LazarevMike/GarMen_StepTracker/Analogue filter/Equations image.png

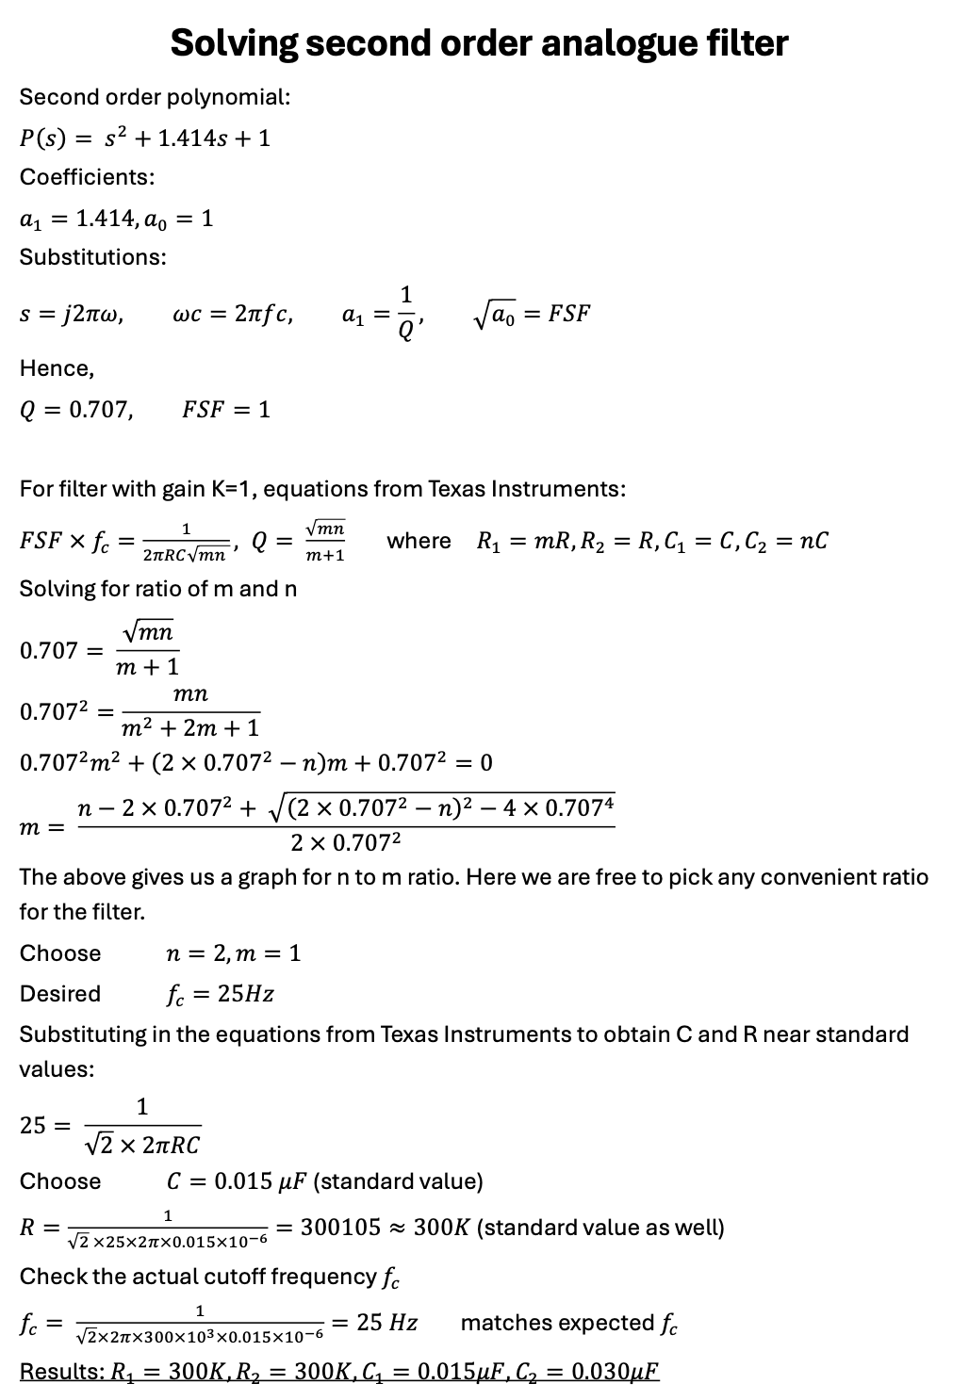
Analogue filter/Equations image.png
