LazarevMike/GarMen_StepTracker/Diagrams/Class Diagram.png

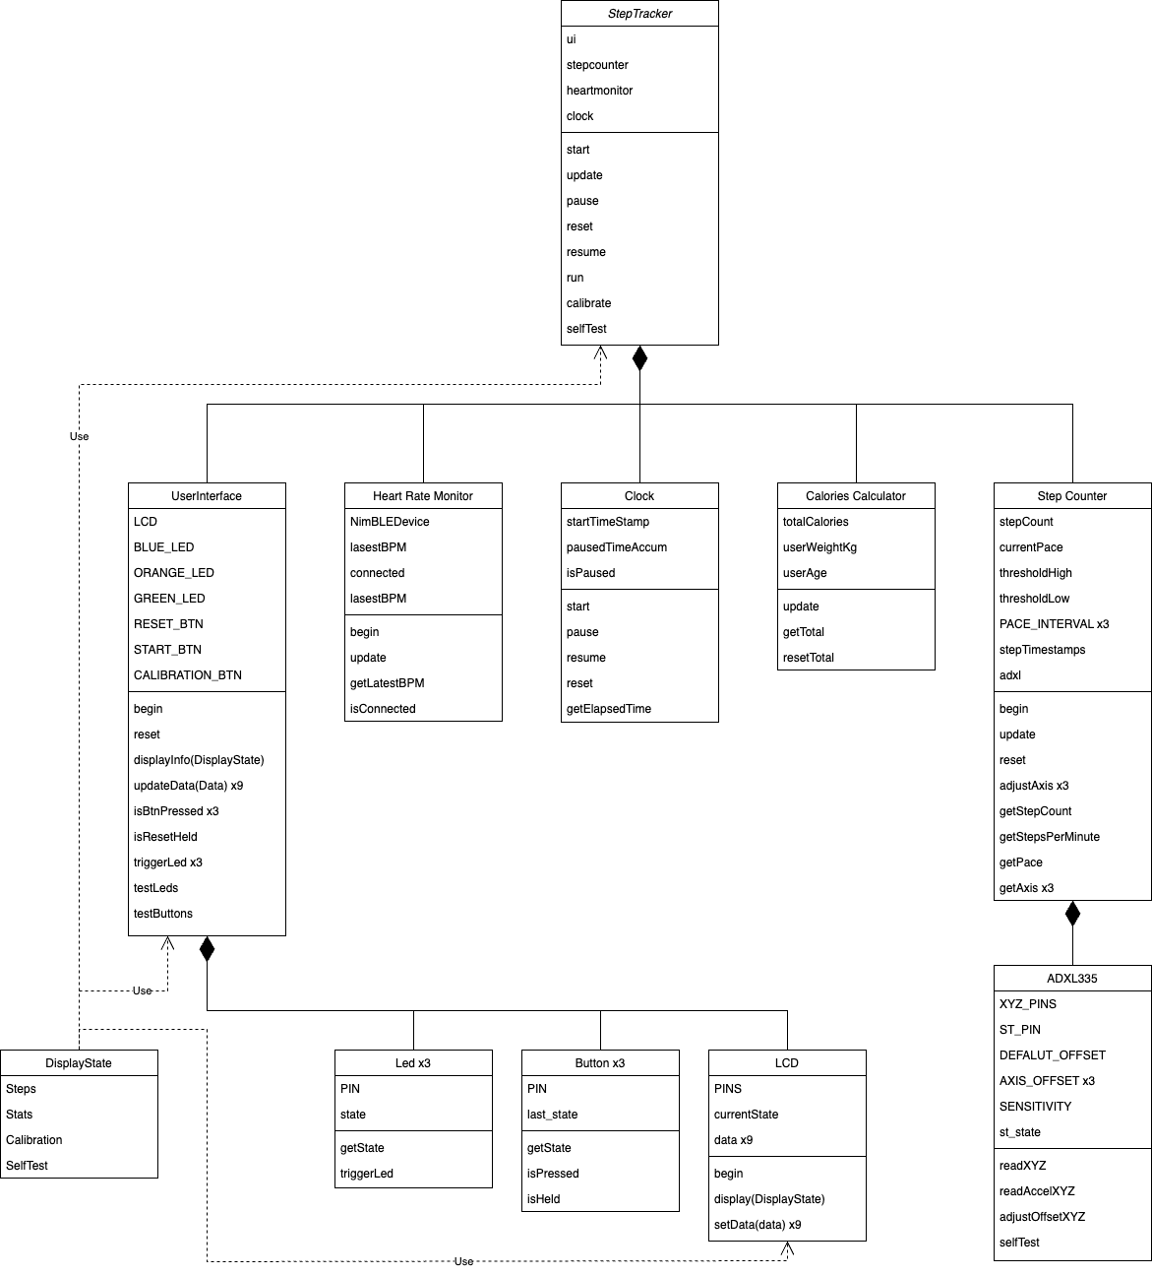
Diagrams/Class Diagram.png
