LazarevMike/GarMen_StepTracker/Diagrams/GarMen Block Diagram Chip.drawio.png

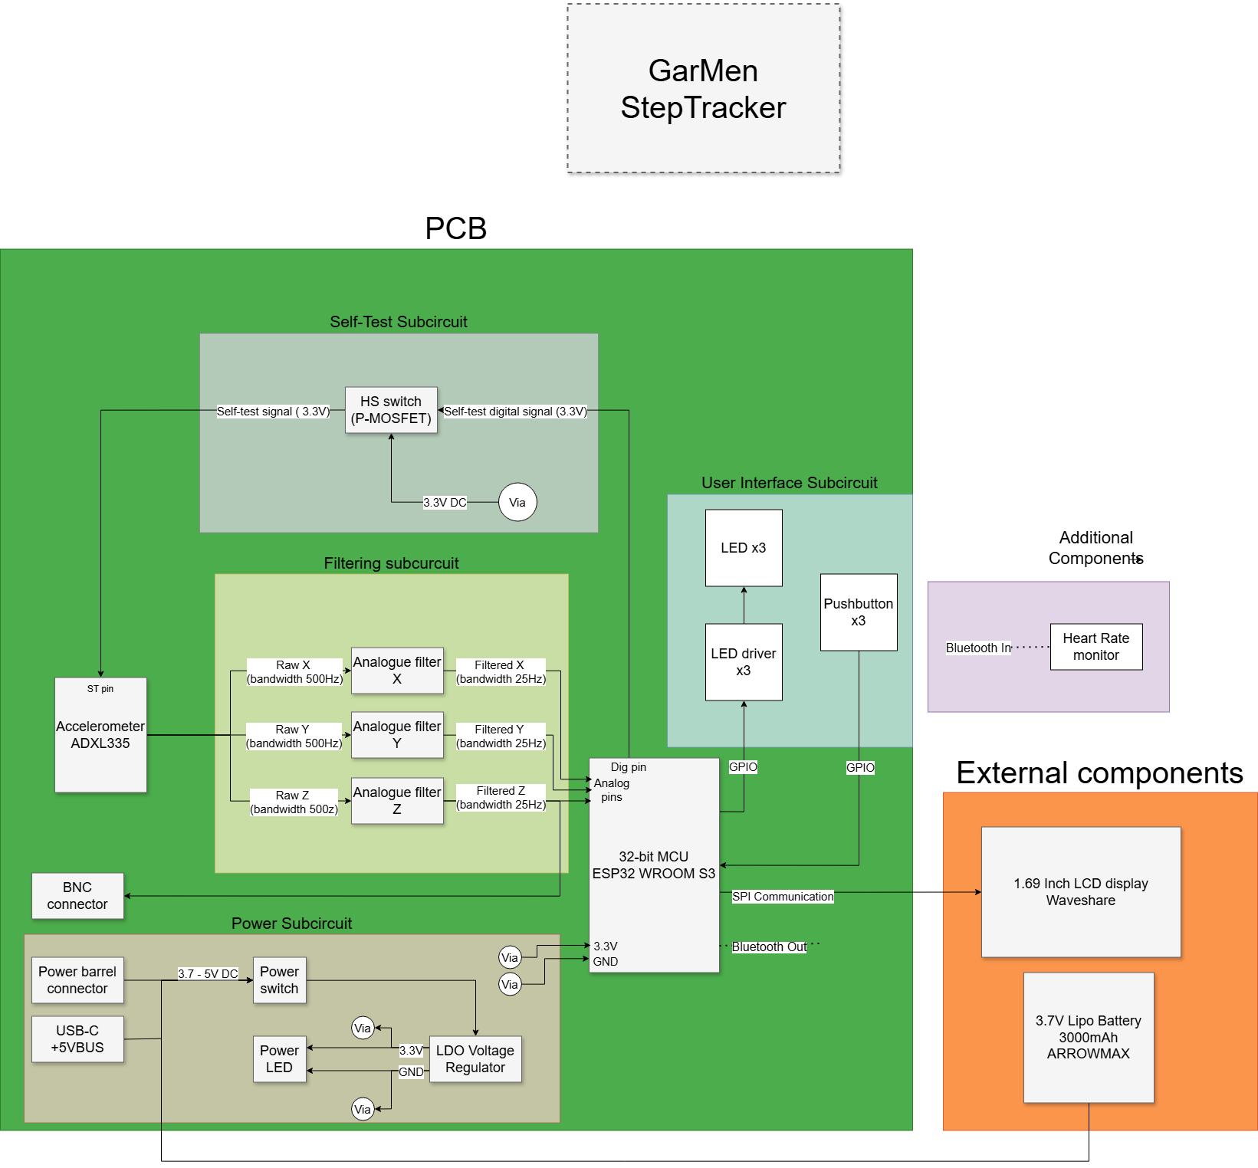
Diagrams/GarMen Block Diagram Chip.drawio.png
