LazarevMike/GarMen_StepTracker/Simulations/Analogue filter/Ideal model/Cutoff frequency.png

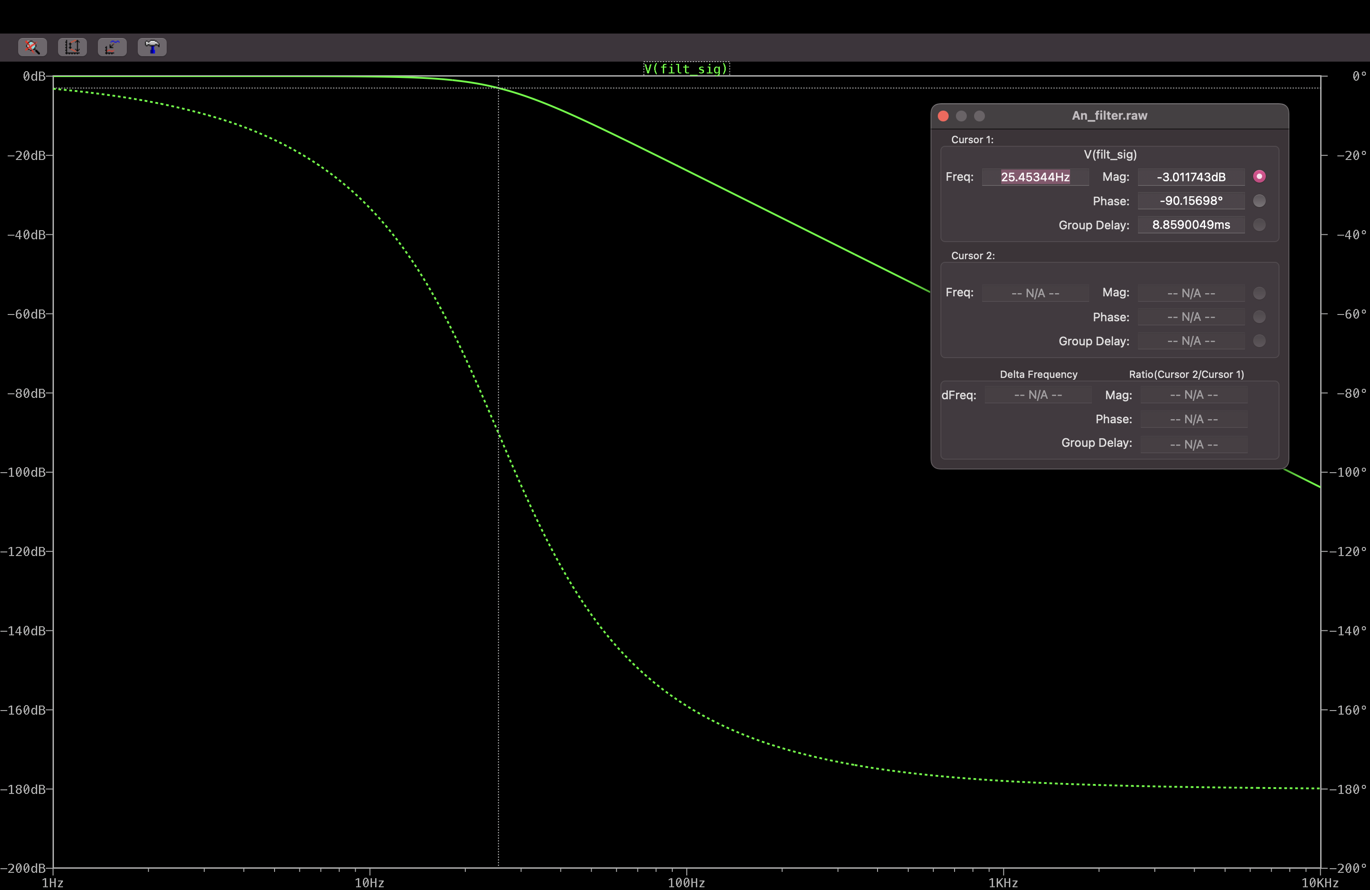
Simulations/Analogue filter/Ideal model/Cutoff frequency.png
