LazarevMike/GarMen_StepTracker/Simulations/Analogue filter/Ideal model/Graph.png

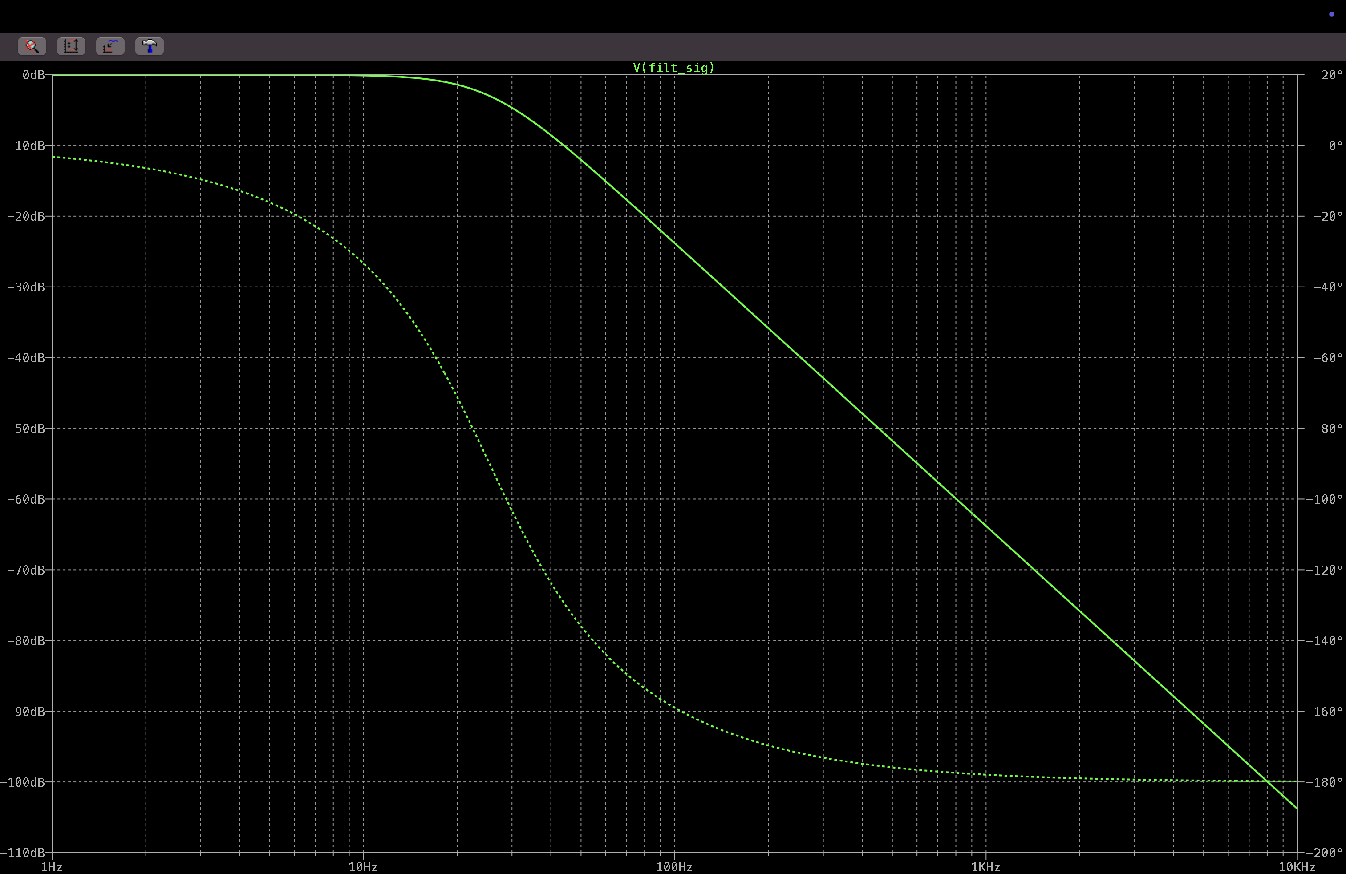
Simulations/Analogue filter/Ideal model/Graph.png
