LazarevMike/GarMen_StepTracker/Simulations/Analogue filter/Ideal model/Overall.png

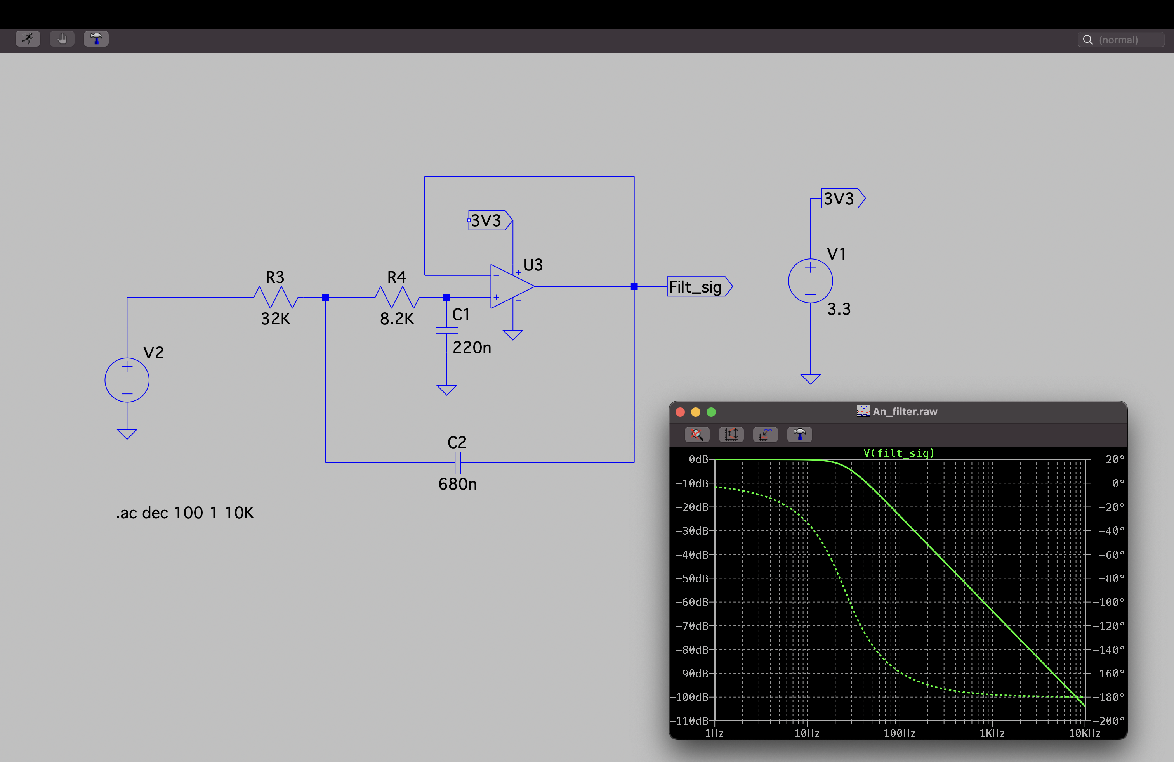
Simulations/Analogue filter/Ideal model/Overall.png
