LazarevMike/GarMen_StepTracker/Simulations/Analogue filter/Real model/Cutoff active.png

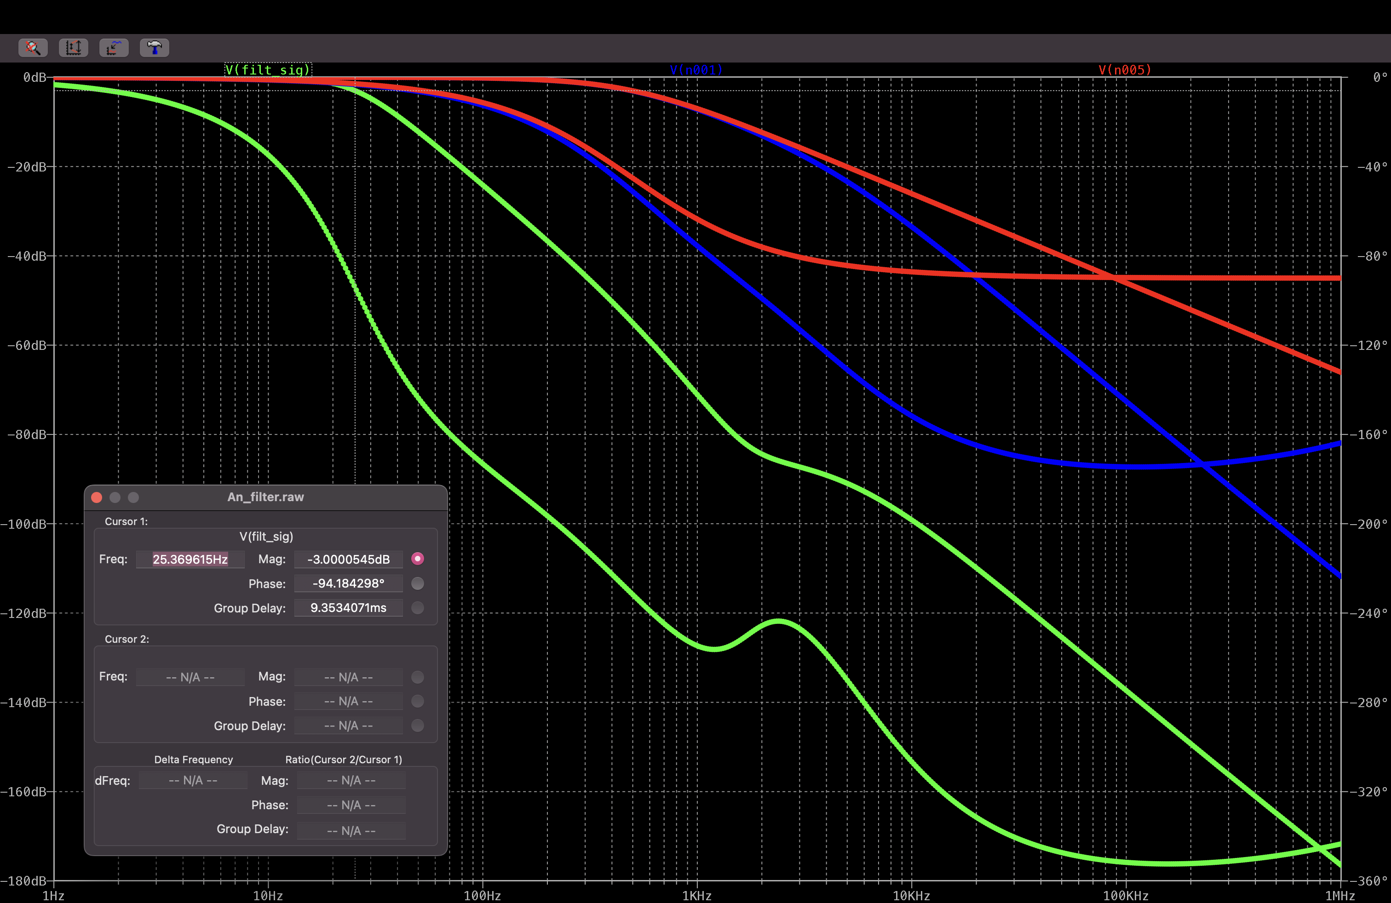
Simulations/Analogue filter/Real model/Cutoff active.png
