LazarevMike/GarMen_StepTracker/Simulations/Analogue filter/Real model/Graph.png

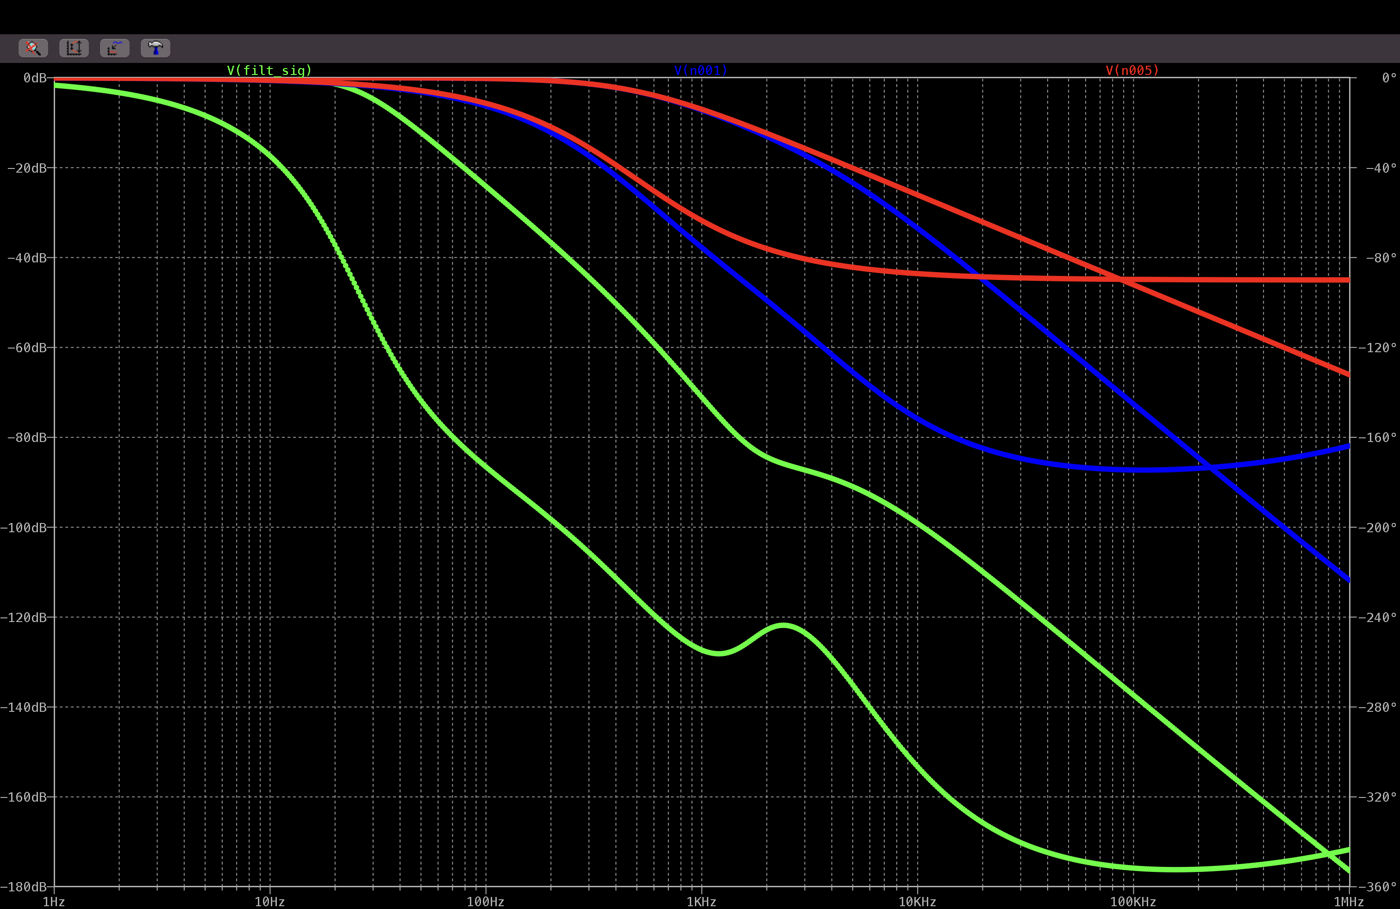
Simulations/Analogue filter/Real model/Graph.png
