LazarevMike/GarMen_StepTracker/Simulations/Analogue filter/Real model/tran 10Hz.png

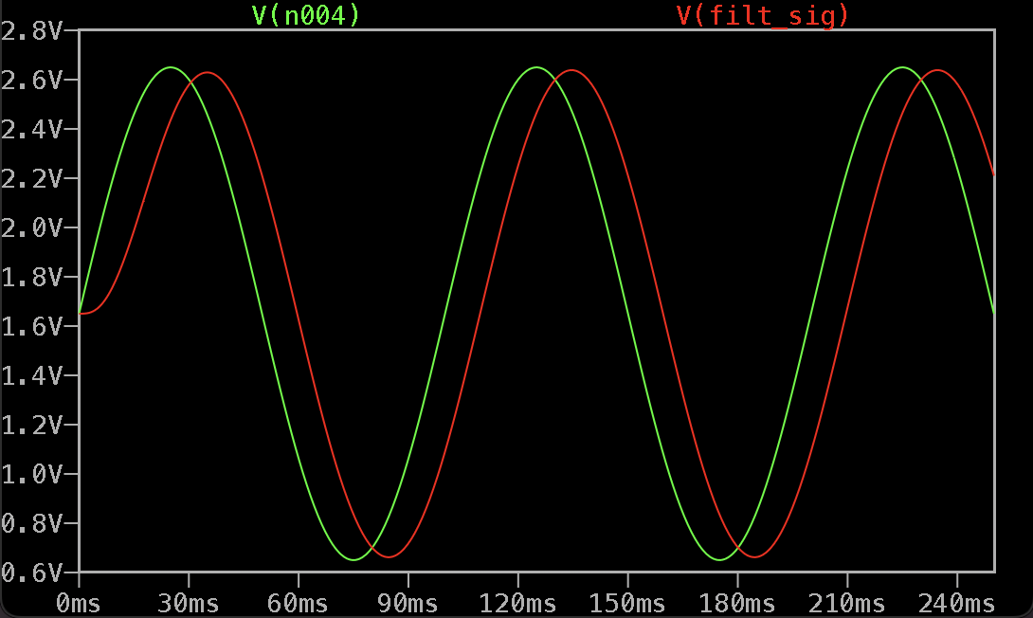
Simulations/Analogue filter/Real model/tran 10Hz.png
