LazarevMike/GarMen_StepTracker/Simulations/Analogue filter/Real model/tran 25Hz.png

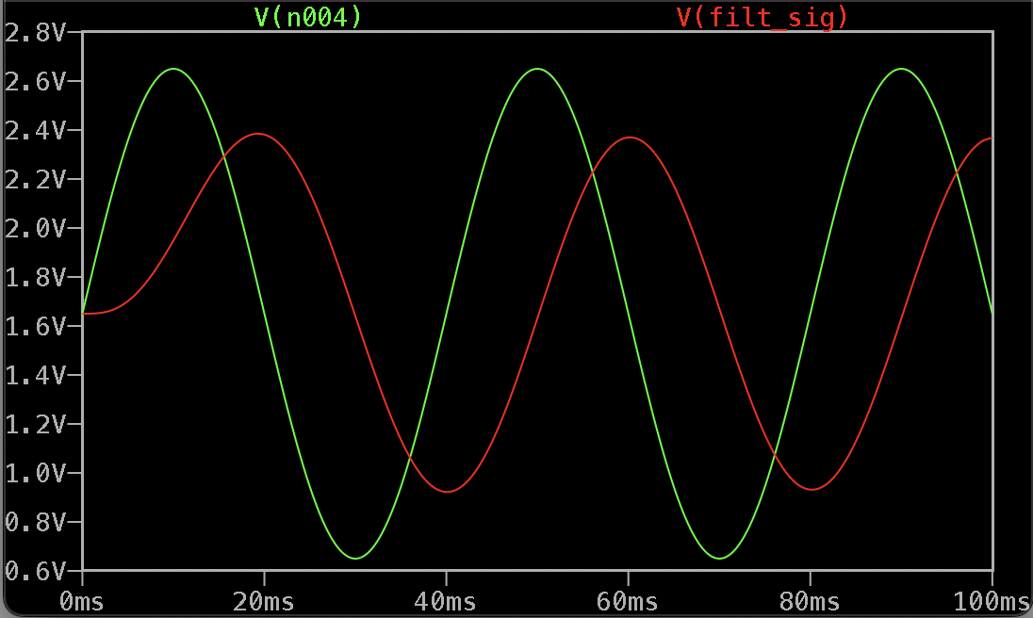
Simulations/Analogue filter/Real model/tran 25Hz.png
