LazarevMike/GarMen_StepTracker/Simulations/Analogue filter/Real model/tran 100Hz.png

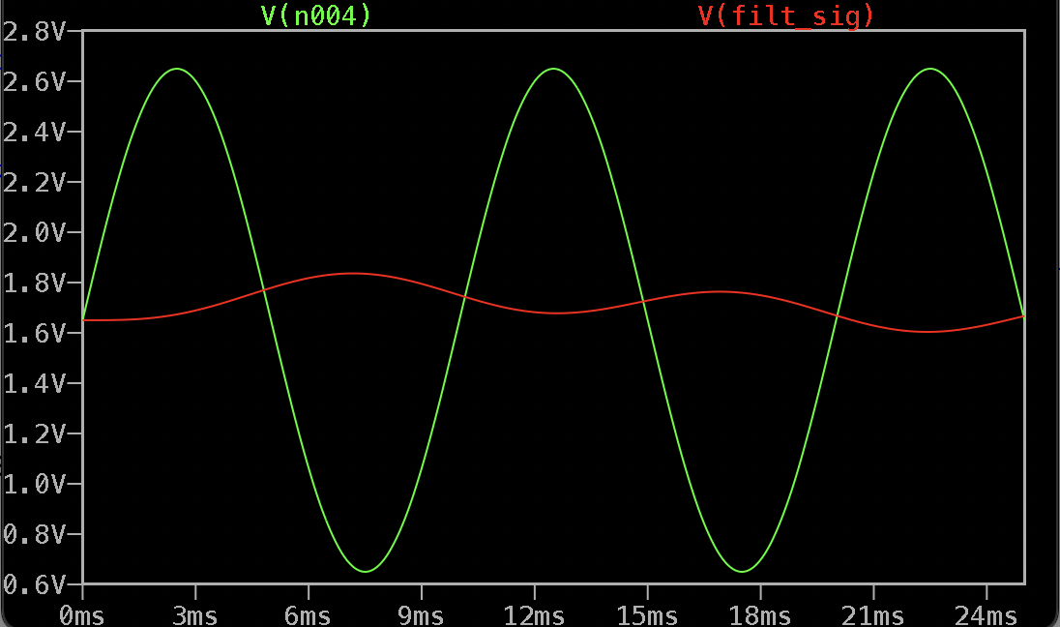
Simulations/Analogue filter/Real model/tran 100Hz.png
