LazarevMike/GarMen_StepTracker/SolidWorks/Enclosure design/PCB.SLDPRT

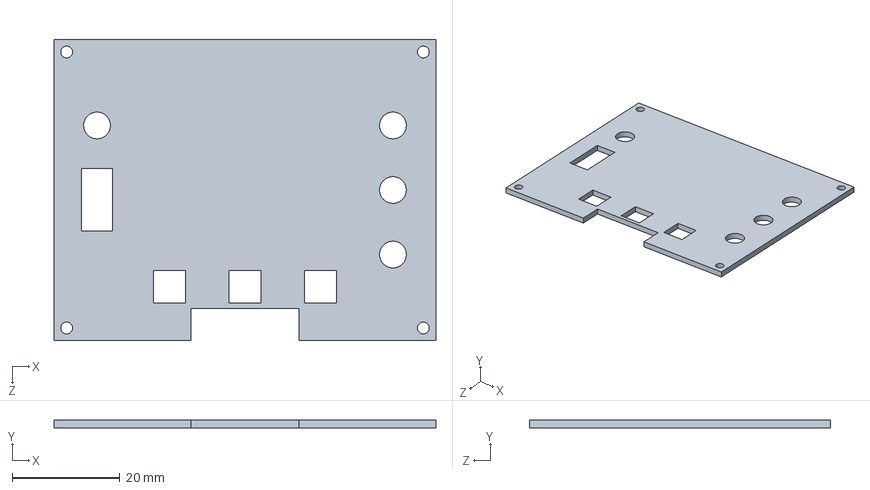
[picture p33: CAD file, 2025-04-03]
SolidWorks/Enclosure design/PCB.SLDPRT
71.0 x 1.50 x 56.0 mm
