LazarevMike/GarMen_StepTracker/SolidWorks/Enclosure design/Battery.SLDPRT

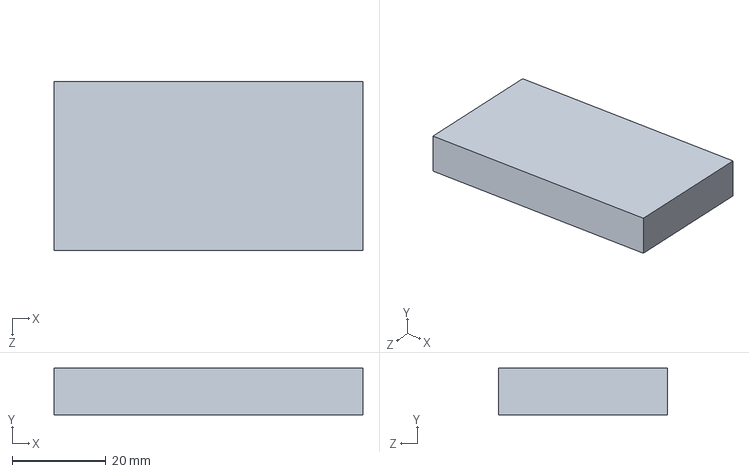
[picture p34: CAD file, 2025-03-20]
SolidWorks/Enclosure design/Battery.SLDPRT
66.0 x 10.0 x 36.0 mm
