LazarevMike/GarMen_StepTracker/SolidWorks/Enclosure design/1_69inch-lcd-module.SLDASM

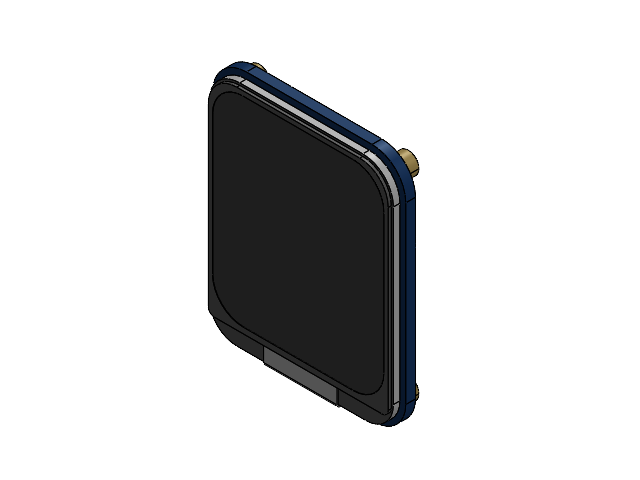
[picture p35: CAD file, 2025-06-17]
SolidWorks/Enclosure design/1_69inch-lcd-module.SLDASM
1_69INCH-240X280-LCD.stp
1_69INCH_LCD_MODULE-PCBA.stp
STUDS-M2XH2_5.stp x 4
