LazarevMike/GarMen_StepTracker/Analogue filter/Real testing/image.png

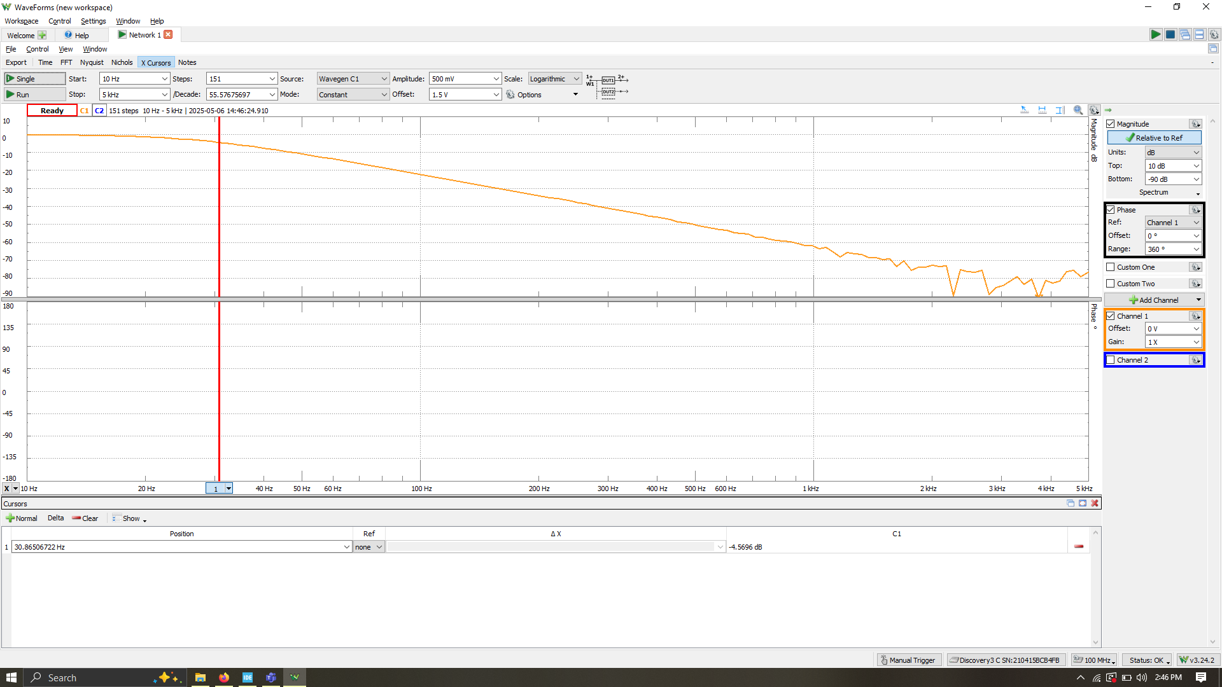
Analogue filter/Real testing/image.png
