LazarevMike/GarMen_StepTracker/Simulations/Self-test driver/ST_HIGH.png

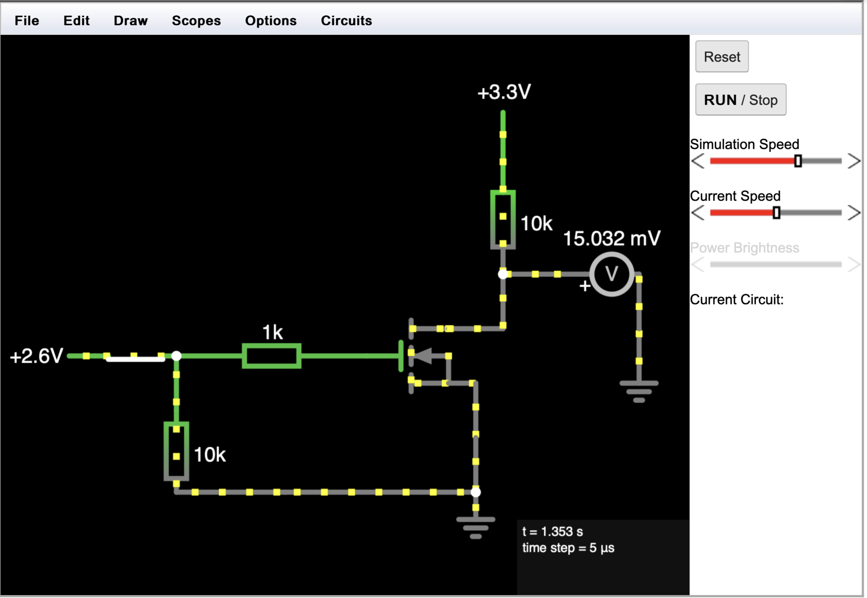
Simulations/Self-test driver/ST_HIGH.png
